krzychb/OnlineHumidifier/6-Chart/pictures/add-humidity-to-feeds-full.png

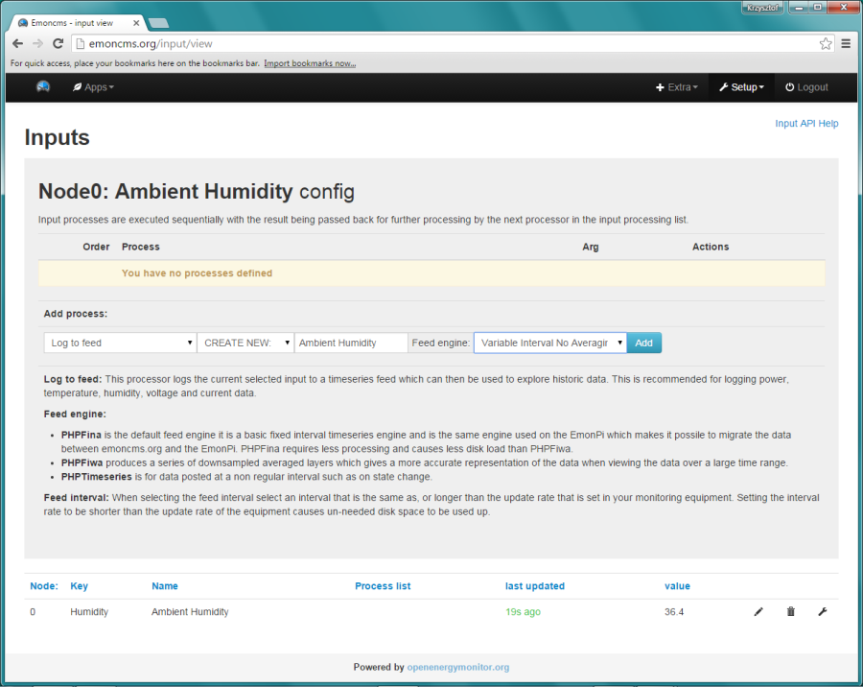
6-Chart/pictures/add-humidity-to-feeds-full.png
