krzychb/OnlineHumidifier/A2-openHAB/pictures/openhab-demo-windows7-chrome.png

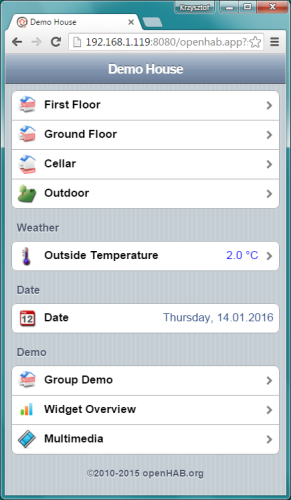
A2-openHAB/pictures/openhab-demo-windows7-chrome.png
