krzychb/OnlineHumidifier/A3-HTTP/pictures/output-on-external-terminal.png

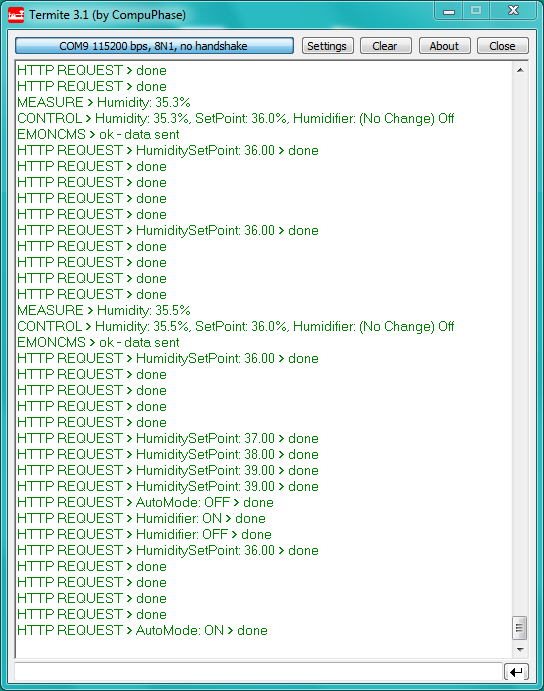
A3-HTTP/pictures/output-on-external-terminal.png
